slash128v6/DC30_CNet_Badge/Docs/images/Picture27.jpg

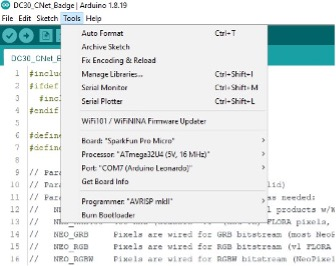
Docs/images/Picture27.jpg
